jonny190/TableLight/docs/images/cone_shade.png

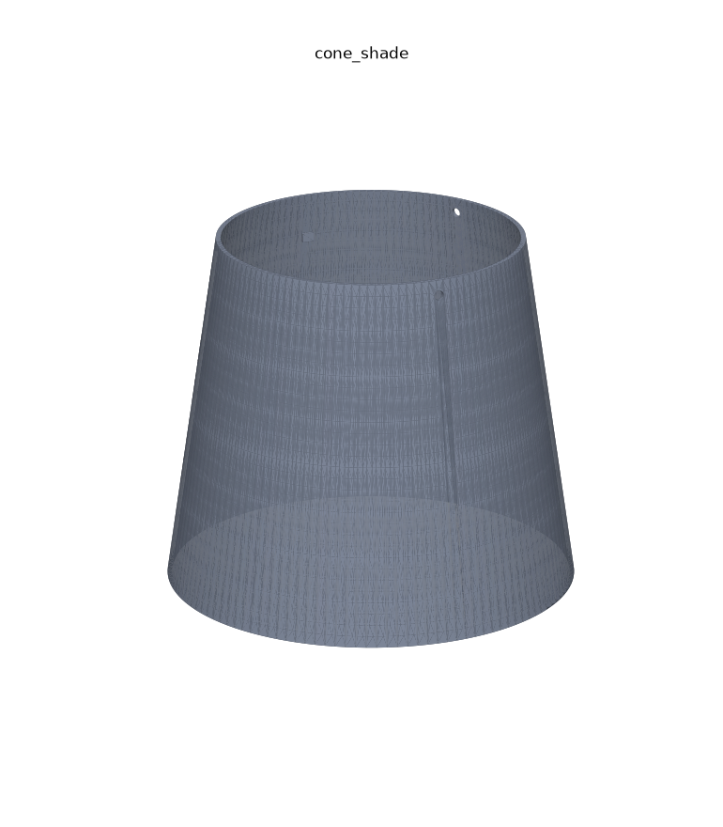
docs/images/cone_shade.png
